Wlinuxhv/water-tower-system/android_app/README.md

# 📱 水塔监控 Android APP

基于 Kotlin 的水塔监控系统 Android 客户端

## 🚀 功能特性

- ✅ **实时水位监控** - 5 秒自动刷新各水塔水位
- ✅ **水泵远程控制** - 手动开启/关闭每个水塔的水泵
- ✅ **自动/手动模式切换** - 智能自动控制或远程手动控制
- ✅ **缺水报警** - 井水缺水时推送通知
- ✅ **历史记录** - 查看水位变化曲线
- ✅ **多水塔管理** - 支持最多 8 个水塔
- ✅ **在线状态显示** - 实时显示从机在线/离线状态

## 📋 系统要求

- Android 8.0 (API 26) 及以上
- WiFi 网络连接
- 存储空间：至少 50MB

## 🔧 编译说明

### 方法 1: Android Studio (推荐)

1. **安装 Android Studio**
   - 下载：https://developer.android.com/studio
   - 安装并打开

2. **打开项目**
   - File → Open
   - 选择 `android_app` 文件夹

3. **等待 Gradle 同步**
   - 首次打开会自动下载依赖
   - 可能需要几分钟

4. **运行 APP**
   - 连接 Android 设备或启动模拟器
   - 点击 Run 按钮 (绿色三角形)

5. **生成 APK**
   - Build → Build Bundle(s) / APK(s) → Build APK(s)
   - APK 位置：`app/build/outputs/apk/debug/app-debug.apk`

### 方法 2: 命令行编译

```bash
cd android_app

# Windows
gradlew.bat assembleDebug

# Linux/Mac
./gradlew assembleDebug

# 生成 Release 版本
./gradlew assembleRelease
```

APK 输出位置：
- Debug: `app/build/outputs/apk/debug/app-debug.apk`
- Release: `app/build/outputs/apk/release/app-release-unsigned.apk`

## 📲 安装说明

### 通过 USB 安装

1. 启用开发者选项：
   - 设置 → 关于手机 → 连续点击"版本号"7 次
2. 启用 USB 调试：
   - 设置 → 开发者选项 → USB 调试
3. 连接手机到电脑
4. 使用 ADB 安装：
   ```bash
   adb install app/build/outputs/apk/debug/app-debug.apk
   ```

### 直接安装 APK

1. 将 APK 传输到手机
2. 在手机文件管理器中点击 APK
3. 允许"未知来源"安装
4. 完成安装

## ⚙️ 配置说明

### 首次使用

1. **打开 APP**
   - 图标：💧 水滴图标
   - 名称：水塔监控

2. **配置 ESP8266 IP 地址**
   - 默认：`http://192.168.4.1` (AP 模式)
   - 或：ESP8266 在你 WiFi 中的 IP (如 `http://192.168.1.100`)
   - 进入 设置 → 服务器地址 → 输入 IP → 保存

3. **连接测试**
   - 返回主界面
   - 下拉刷新
   - 应能看到水塔列表

### 连接模式

**模式 1: AP 模式 (ESP8266 热点)**
- ESP8266 创建 WiFi 热点
- 手机连接该热点
- IP 地址：`192.168.4.1`
- 优点：无需路由器，随时随地连接
- 缺点：手机无法访问互联网

**模式 2: 路由模式 (推荐)**
- ESP8266 连接到你的 WiFi 路由器
- 手机连接同一 WiFi
- IP 地址：路由器分配的 IP (如 `192.168.1.100`)
- 优点：手机可同时访问互联网
- 缺点：需要 WiFi 路由器

## 🎨 界面说明

### 主界面

```
┌─────────────────────────────────┐
│  水塔监控           [设置] [历史]│
├─────────────────────────────────┤
│  模式：自动  |  在线：3/4       │
│  [刷新]                         │
├─────────────────────────────────┤
│  ┌───────────────────────────┐  │
│  │ 水塔 1              45%   │  │
│  │ ████████.......... [泵]   │  │
│  │ 在线 | 自动 | 正常        │  │
│  └───────────────────────────┘  │
│  ┌───────────────────────────┐  │
│  │ 水塔 2              78%   │  │
│  │ ██████████████....        │  │
│  │ 在线 | 自动 | 正常        │  │
│  └───────────────────────────┘  │
└─────────────────────────────────┘
```

### 水泵控制对话框

点击任意水塔卡片：
- 显示当前水位
- 开启/关闭水泵按钮
- 确认操作

### 设置界面

- **服务器地址**: ESP8266 的 IP 地址
- **刷新间隔**: 5-60 秒
- **通知开关**: 报警通知
- **关于**: 版本信息

### 历史记录界面

- 日期选择器
- 水位变化曲线图
- 最高/最低水位统计

## 🔌 API 接口

APP 通过 REST API 与 ESP8266 通信：

### 获取状态
```
GET /api/status
Response:
{
  "mode": 0,
  "wifi": true,
  "well_water": true,
  "towers": [
    {
      "id": 1,
      "level": 45,
      "pump": false,
      "online": true
    }
  ]
}
```

### 控制水泵
```
POST /api/pump
Body: tower=1&action=on
Response: OK
```

### 切换模式
```
POST /api/mode
Body: mode=0 (自动) 或 mode=1 (手动)
Response: OK
```

## 🐛 故障排查

### 问题：无法连接到服务器

**可能原因:**
- IP 地址错误
- 手机和 ESP8266 不在同一网络
- ESP8266 未启动 Web 服务器

**解决方法:**
1. 检查 IP 地址是否正确
2. 确认手机连接正确的 WiFi
3. 在浏览器访问 `http://IP/api/status` 测试
4. 检查 ESP8266 串口日志

### 问题：数据刷新失败

**可能原因:**
- WiFi 信号弱
- ESP8266 处理不过来
- 从机离线

**解决方法:**
1. 增加刷新间隔 (设置 → 刷新间隔)
2. 检查水塔在线状态
3. 重启 ESP8266

### 问题：水泵控制无响应

**可能原因:**
- 从机离线
- LoRa 通信故障
- 继电器损坏

**解决方法:**
1. 检查从机在线状态
2. 查看 ESP8266 串口日志
3. 手动测试继电器

## 📦 依赖库

```gradle
// AndroidX
implementation 'androidx.core:core-ktx:1.12.0'
implementation 'androidx.appcompat:appcompat:1.6.1'
implementation 'com.google.android.material:material:1.11.0'
implementation 'androidx.constraintlayout:constraintlayout:2.1.4'
implementation 'androidx.lifecycle:lifecycle-runtime-ktx:2.7.0'

// RecyclerView
implementation 'androidx.recyclerview:recyclerview:1.3.2'

// Retrofit (HTTP 客户端)
implementation 'com.squareup.retrofit2:retrofit:2.9.0'
implementation 'com.squareup.retrofit2:converter-gson:2.9.0'
implementation 'com.squareup.okhttp3:logging-interceptor:4.12.0'

// MPAndroidChart (图表)
implementation 'com.github.PhilJay:MPAndroidChart:v3.1.0'
```

## 📝 开发说明

### 项目结构

```
app/src/main/java/com/watertower/monitor/
├── MainActivity.kt      # 主界面
├── ApiService.kt        # API 接口定义
├── ApiClient.kt         # API 客户端管理器
├── TowerAdapter.kt      # 水塔列表适配器
├── models.kt            # 数据模型
├── SettingsActivity.kt  # 设置界面
└── HistoryActivity.kt   # 历史记录界面
```

### 添加新功能

1. **添加新的 API 接口**
   - 编辑 `ApiService.kt`
   - 添加接口方法

2. **添加新的数据字段**
   - 编辑 `models.kt`
   - 在 `TowerData` 类中添加字段

3. **更新 UI**
   - 编辑对应的 Activity 或 Adapter
   - 修改布局文件

### 编译发布版本

```bash
# 1. 修改 app/build.gradle 中的 versionCode 和 versionName
# 2. 生成签名密钥 (首次)
keytool -genkey -v -keystore watertower.keystore -alias watertower -keyalg RSA -keysize 2048 -validity 10000

# 3. 在 gradle.properties 中配置签名
# 4. 编译 Release 版本
./gradlew assembleRelease

# 5. APK 位置
app/build/outputs/apk/release/app-release.apk
```

## 📄 许可证

MIT License

## 👥 贡献

欢迎提交 Issue 和 Pull Request!

---

**版本**: 1.0.0  
**作者**: Wlinuxhv  
**更新**: 2026-02-28
