Wlinuxhv/water-tower-system/PROJECT_STATUS.md

# 📊 项目完成状态

**更新日期**: 2026-02-28  
**版本**: v1.0.0

---

## ✅ 已完成的工作

### 0. 本次更新 (2026-02-28)

| 功能 | 说明 | 状态 |
|---|---|---|
| **Android 历史曲线图** | MPAndroidChart 集成，支持日期选择、水位曲线、统计信息 | ✅ 完成 |
| **ESP8266 历史记录** | 每小时自动保存，循环缓冲区存储 48 小时数据 | ✅ 完成 |
| **API 扩展** | `/api/history` 接口，支持按水塔 ID 和时间查询 | ✅ 完成 |

### 1. GitHub 仓库创建

| 仓库 | URL | 状态 |
|---|-----|---|
| **水塔监控系统** | https://github.com/Wlinuxhv/water-tower-system | ✅ 已发布 v1.0.0 |
| **PAN3031 驱动** | https://github.com/Wlinuxhv/pan3031-stc32g | ✅ 已有 73 次构建 |

### 2. 代码文件

#### 水塔监控系统 (water-tower-system)

| 目录/文件 | 内容 | 状态 |
|---|---|---|
| `README.md` | 系统说明、硬件清单、快速开始 | ✅ |
| `esp8266_master/src/main.cpp` | ESP8266 主机程序 | ✅ |
| `esp8266_master/src/water_system.h` | 数据结构定义 | ✅ |
| `esp8266_master/platformio.ini` | PlatformIO 配置 | ✅ |
| `slave_node/src/main.c` | STC32G 从机程序 | ✅ |
| `slave_node/Makefile` | SDCC 编译配置 | ✅ |
| `android_app/` | Android APP (完整) | ✅ |
| `android_app/README.md` | APP 编译和使用说明 | ✅ |
| `docs/系统设计文档.md` | 完整设计文档 | ✅ |
| `docs/硬件接线图.md` | 详细接线图 | ✅ |
| `docs/快速开始指南.md` | 5 分钟上手指南 | ✅ |
| `.github/workflows/android-ci.yml` | Android CI/CD | ✅ |
| `.github/workflows/embedded-ci.yml` | 嵌入式 CI/CD | ✅ |
| `.gitignore` | Git 忽略配置 | ✅ |

#### PAN3031 驱动 (pan3031-stc32g)

| 内容 | 状态 |
|---|---|
| PAN3031 LoRa 驱动 | ✅ |
| HAL 层 (GPIO/UART/SPI/Delay) | ✅ |
| Keil 和 SDCC 编译配置 | ✅ |
| CI/CD 工作流 | ✅ |
| 完整文档 | ✅ |

### 3. 文档

| 文档 | 位置 | 状态 |
|---|---|---|
| 系统设计文档 | `docs/系统设计文档.md` | ✅ |
| 硬件接线图 | `docs/硬件接线图.md` | ✅ |
| 快速开始指南 | `docs/快速开始指南.md` | ✅ |
| README | `README.md` | ✅ |
| Android APP 说明 | `android_app/README.md` | ✅ |

### 4. CI/CD 配置

| 工作流 | 触发条件 | 状态 |
|---|---|---|
| Android CI | android_app 目录推送 | ✅ |
| Embedded CI | esp8266/slave_node推送 | ✅ |
| 自动 Release | 创建标签时 | ✅ |

### 5. GitHub Release

- **水塔监控系统**: v1.0.0 已发布
  - URL: https://github.com/Wlinuxhv/water-tower-system/releases/tag/v1.0.0
  
- **PAN3031 驱动**: 已有多个构建版本
  - URL: https://github.com/Wlinuxhv/pan3031-stc32g/releases

---

## 📋 待完成的工作

### 高优先级 🔴

- [ ] **PCB 设计**
  - 主机 PCB (ESP8266 + LoRa + OLED)
  - 从机 PCB (STC32G + LoRa + 继电器)
  - Gerber 文件输出

- [ ] **3D 外壳设计**
  - 主机外壳
  - 从机外壳 (防水)
  - STL 文件用于 3D 打印

- [ ] **实际硬件测试**
  - 购买元器件
  - 焊接测试
  - 通信距离测试
  - 防水测试

### 中优先级 🟡

- [ ] **Android APP 完善**
  - [x] 水位历史曲线图 ✅ **已完成**
  - [ ] 推送通知
  - [ ] 多语言支持
  - [ ] 深色主题

- [ ] **嵌入式功能增强**
  - [ ] EEPROM 配置保存
  - [ ] OTA 远程升级
  - [ ] 低功耗模式
  - [ ] 看门狗保护

- [ ] **文档完善**
  - [ ] 视频教程
  - [ ] 常见问题 FAQ
  - [ ] 故障排查指南
  - [ ] 英文文档

### 低优先级 🟢

- [ ] **云端集成**
  - [ ] MQTT 服务器连接
  - [ ] 微信小程序
  - [ ] Web 管理界面
  - [ ] 数据分析和报表

- [ ] **功能扩展**
  - [ ] 流量计支持
  - [ ] 电表集成
  - [ ] 太阳能供电
  - [ ] 4G 远程通信

---

## 🎯 下一步行动

### 立即可做 (无需硬件)

1. ✅ **完善 Android APP**
   - [x] 添加 MPAndroidChart 图表库
   - [x] 实现历史记录界面
   - [ ] 优化 UI/UX

2. ✅ **代码审查和优化**
   - 添加更多注释
   - 代码格式化
   - 错误处理增强

3. ✅ **文档翻译**
   - 英文 README
   - 英文文档

### 需要硬件

1. 🔲 **采购元器件**
   - ESP8266 开发板 × 1
   - STC32G12K128 × N (根据水塔数量)
   - PAN3031 LoRa 模块 × (N+1)
   - OLED 显示屏 × 1
   - 液位传感器 × N
   - 继电器模块 × N
   - 缺水传感器 × (N+1)

2. 🔲 **焊接和测试**
   - 主机焊接
   - 从机焊接
   - 通信测试
   - 功能验证

3. 🔲 **现场部署**
   - 水塔安装
   - 接线和固定
   - 系统联调
   - 长期运行测试

---

## 📊 项目统计

### 代码统计

| 语言 | 文件数 | 代码行数 |
|---|---|---|
| C++ (ESP8266) | 2 | ~500 |
| C (STC32G) | 1 | ~300 |
| Kotlin (Android) | 8 | ~950 |
| 文档 | 6 | ~2200 |
| **总计** | **17** | **~3950** |

### 成本估算 (1 主 4 从)

| 项目 | 单价 | 数量 | 小计 |
|---|---|---|---|
| 主机 | ¥145 | 1 | ¥145 |
| 从机 | ¥245 | 4 | ¥980 |
| 水泵 (自备) | ¥300 | 4 | ¥1200 |
| 水管阀门 (自备) | ¥200 | 1 | ¥200 |
| **总计** | | | **¥2,525** |

### 时间估算

| 阶段 | 预计时间 |
|---|---|
| PCB 设计 | 1 周 |
| 外壳设计 | 3 天 |
| 硬件采购 | 1 周 |
| 焊接测试 | 3 天 |
| 系统联调 | 1 周 |
| 现场部署 | 2 天 |
| **总计** | **约 4 周** |

---

## 🌟 项目亮点

1. **完全开源** - 硬件设计、嵌入式代码、APP 全部开源
2. **低成本** - 相比商业方案成本降低 70%+
3. **易扩展** - 支持最多 254 个从机节点
4. **远距离** - LoRa 通信距离 1-3km
5. **双模式** - 自动智能控制 + 远程手动控制
6. **高可靠** - 双重缺水保护，防止水泵烧毁
7. **本地化** - 完整中文文档和技术支持

---

## 📞 联系方式

- **GitHub**: https://github.com/Wlinuxhv
- **Issues**: https://github.com/Wlinuxhv/water-tower-system/issues
- **Discussions**: https://github.com/Wlinuxhv/water-tower-system/discussions

---

**感谢使用！🎉**

如有问题或建议，欢迎在 GitHub 上提 Issue 或参与讨论。
