Wlinuxhv/water-tower-system/slave_node_stc8g/inc/pan3031.h

/*
 * PAN3031 LoRa 模块驱动 - STC8G1K08 版
 * 
 * 特性:
 * - SPI 通信
 * - 低功耗睡眠模式
 * - WOR (Watch On Receiver) 支持
 */

#ifndef PAN3031_H
#define PAN3031_H

#include "slave_config.h"

// ==================== PAN3031 寄存器 ====================
#define REG_FIFO            0x00
#define REG_OP_MODE         0x01
#define REG_FRF_MSB         0x06
#define REG_FRF_MID         0x07
#define REG_FRF_LSB         0x08
#define REG_PA_CONFIG       0x09
#define REG_LNA             0x0C
#define REG_FIFO_ADDR_PTR   0x0D
#define REG_FIFO_TX_BASE    0x0E
#define REG_FIFO_RX_BASE    0x0F
#define REG_FIFO_RX_ADDR    0x10
#define REG_IRQ_FLAGS       0x12
#define REG_RX_NB_BYTES     0x13
#define REG_PKT_SNR         0x19
#define REG_PKT_RSSI        0x1A
#define REG_MODEM_CONFIG1   0x1D
#define REG_MODEM_CONFIG2   0x1E
#define REG_PREAMBLE        0x20
#define REG_PAYLOAD_LEN     0x22
#define REG_FIFO_RX_BYTE    0x26
#define REG_MODEM_CONFIG3   0x26
#define REG_RSSI_WIDEBAND   0x2C
#define REG_OSC             0x24
#define REG_SYNC_WORD       0x39
#define REG_INVERTIQ        0x33
#define REG_DIO_MAPPING1    0x40
#define REG_VERSION         0x42
#define REG_AGC_REF         0x61
#define REG_AGC_THRESH1     0x62
#define REG_AGC_THRESH2     0x63
#define REG_AGC_THRESH3     0x64
#define REG_PLL_HOP         0x44
#define REG_TCXO            0x58
#define REG_PA_DAC          0x5A
#define REG_FORMER_TEMP     0x6C
#define REG_BIT_RATE_FRAC   0x5D

// 工作模式
#define MODE_SLEEP          0x00
#define MODE_STDBY          0x01
#define MODE_FSTX           0x02
#define MODE_TX             0x03
#define MODE_FSRX           0x04
#define MODE_RXCONT         0x05
#define MODE_RXSINGLE       0x06

// ==================== 函数声明 ====================
void pan3031_init(void);
void pan3031_write_reg(uint8_t addr, uint8_t value);
uint8_t pan3031_read_reg(uint8_t addr);
void pan3031_set_freq(uint32_t freq);
void pan3031_set_sf(uint8_t sf);
void pan3031_set_bw(uint32_t bw);
void pan3031_set_power(uint8_t power);
void pan3031_send(uint8_t *data, uint8_t len);
uint8_t pan3031_receive(uint8_t *data, uint8_t *len);
void pan3031_sleep(void);
void pan3031_wor_enable(void);

#endif
